kamibababa/mix-fpga/dev/mov/wtf.png

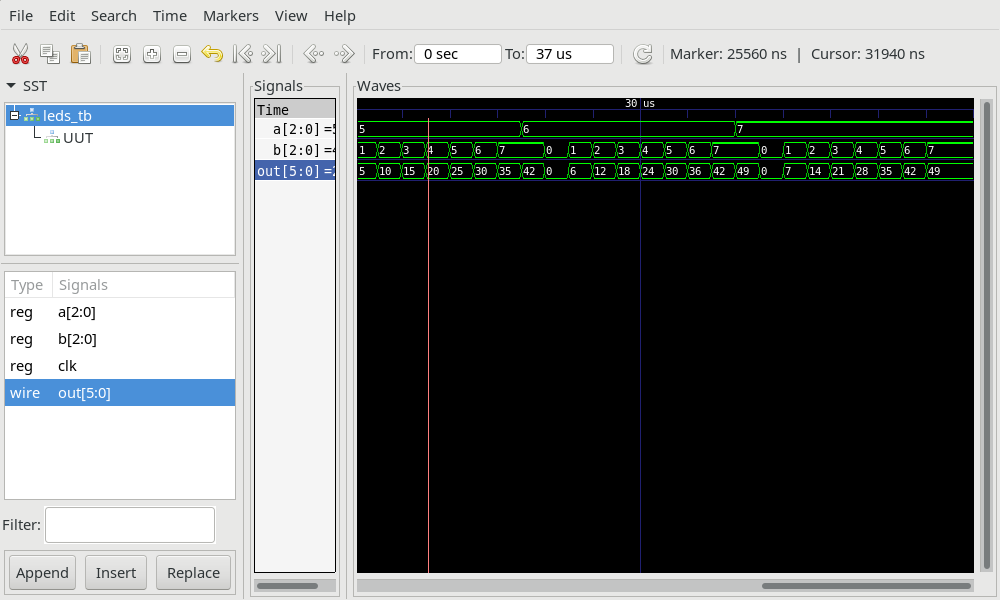
dev/mov/wtf.png
