kamibababa/mix-fpga/mixal/1.3.2.ex20/t.png

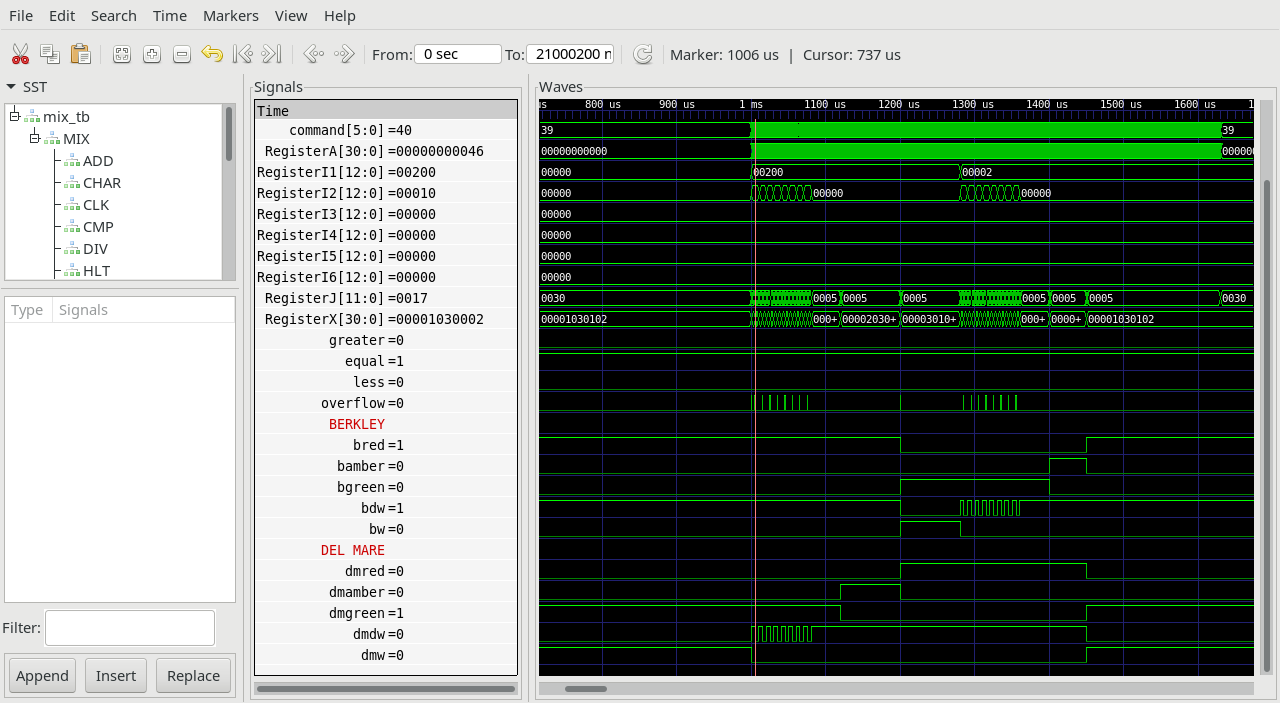
mixal/1.3.2.ex20/t.png
