kamibababa/mix-fpga/mix/mul2.v

//------------------------------------------------------------------
//-- Hello world example
//-- Control leds by pushing the buttons
//-- This example has been tested on the following boards:
//--   * iCE40-HX1K-EVB Olimex
//------------------------------------------------------------------

module mul2(
	input wire clk,
	input wire start,
	output reg stop,
	input wire [29:0] a,
	input wire [29:0] b,
	output wire [59:0] out
	);
assign out = s50[59:0];
reg [31:0] s0;
reg [31:0] s1;
reg [31:0] s2;
reg [31:0] s3;
reg [31:0] s4;
reg [31:0] s5;
reg [31:0] s6;
reg [31:0] s7;
reg [31:0] s8;
reg [31:0] s9;
reg [31:0] s10;
reg [31:0] s11;
reg [31:0] s12;
reg [31:0] s13;
reg [31:0] s14;


always @(posedge clk)
	if (start) s0 <= (b[0]? 
					(b[1]?
						({2'b0,a[29:0]}+{1'b0,a[29:0],1'b0}):
						({2'b0,a[29:0]})):
					(b[1]?
						({1'b0,a[29:0],1'b0}):
						(32'b0)));
	else s0 <= 32'b0;
always @(posedge clk)
	if (start) s1 <= (b[2]? 
					(b[3]?
						({2'b0,a[29:0]}+{1'b0,a[29:0],1'b0}):
						({2'b0,a[29:0]})):
					(b[3]?
						({1'b0,a[29:0],1'b0}):
						(32'b0)));
	else s1 <= 32'b0;
always @(posedge clk)
	if (start) s2 <= (b[4]? 
					(b[5]?
						({2'b0,a[29:0]}+{1'b0,a[29:0],1'b0}):
						({2'b0,a[29:0]})):
					(b[5]?
						({1'b0,a[29:0],1'b0}):
						(32'b0)));
	else s2 <= 32'b0;
always @(posedge clk)
	if (start) s3 <= (b[6]? 
					(b[7]?
						({2'b0,a[29:0]}+{1'b0,a[29:0],1'b0}):
						({2'b0,a[29:0]})):
					(b[7]?
						({1'b0,a[29:0],1'b0}):
						(32'b0)));
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

always @(posedge clk)
	if (stage4) s40 <= {9'd0 , s30} + {1'd0,s31,8'd0};
	else s40 <= 49'b0;
always @(posedge clk)
	if (stage4) s41 <= {9'd0 , s32} + {1'd0,s33,8'd0};
	else s41 <= 49'b0;
//stage5	
reg [65:0] s50;

reg stage5;
always @(posedge clk)
	if (stage4) stage5 <= 1;
	else stage5 <= 0;

always @(posedge clk)
	if (stage5) s50 <= {17'd0 , s40} + {1'd0,s41,16'd0};
	else s50 <= 66'b0;

always @(posedge clk)
	if (stage5) stop <=1;
	else stop <=0;
endmodule
